StonedEdge/Retro-Lite-CM4/CAD Files/Housing/Screen Bezel Dimensions (Glass - Tempered).PNG

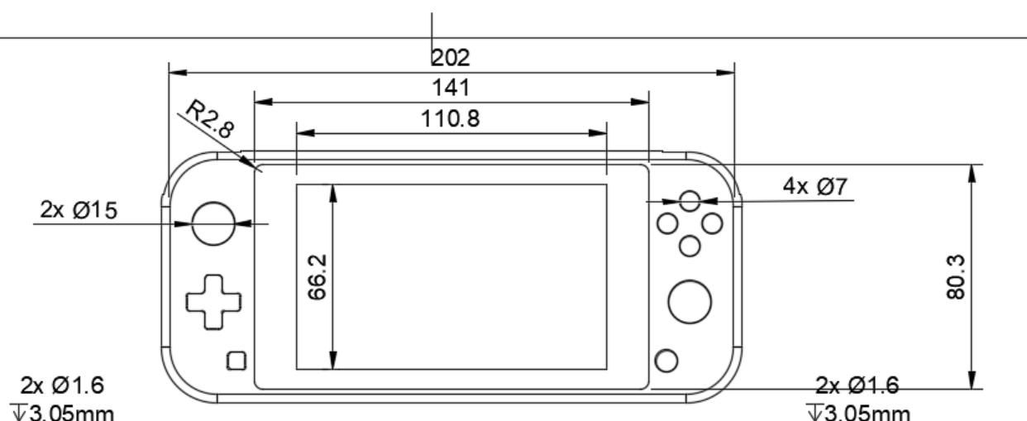
CAD Files/Housing/Screen Bezel Dimensions (Glass - Tempered).PNG
