StonedEdge/Retro-Lite-CM4/keyboard/00.png

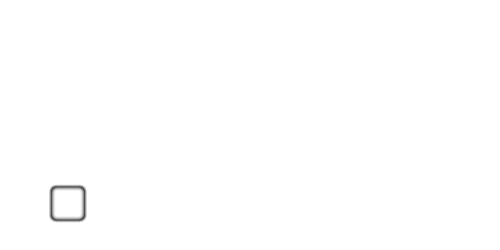
keyboard/00.png
