StonedEdge/Retro-Lite-CM4/keyboard/02.png

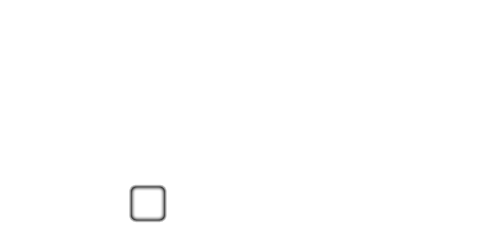
keyboard/02.png
