StonedEdge/Retro-Lite-CM4/keyboard/03.png

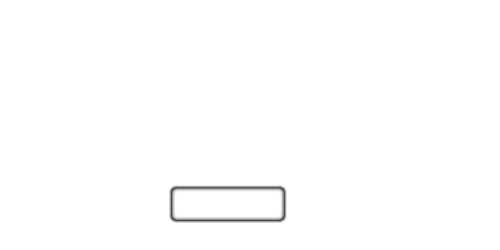
keyboard/03.png
