StonedEdge/Retro-Lite-CM4/keyboard/05.png

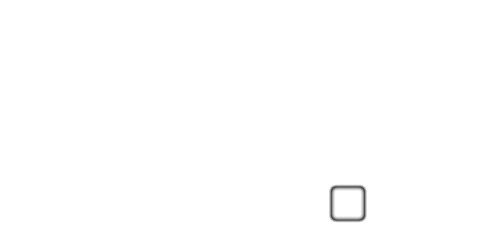
keyboard/05.png
