StonedEdge/Retro-Lite-CM4/keyboard/06.png

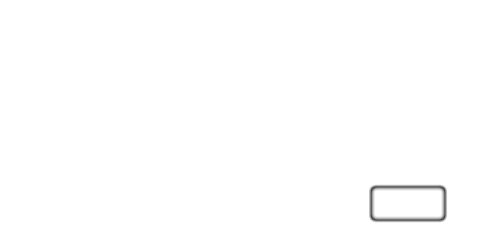
keyboard/06.png
