StonedEdge/Retro-Lite-CM4/keyboard/11.png

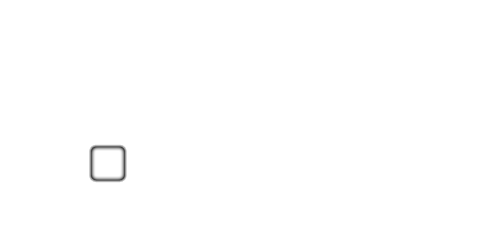
keyboard/11.png
