StonedEdge/Retro-Lite-CM4/keyboard/13.png

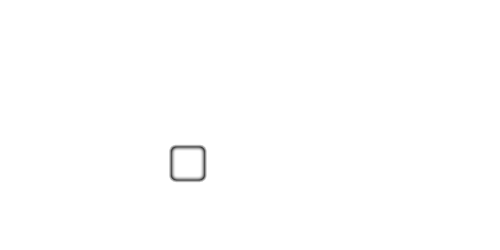
keyboard/13.png
