StonedEdge/Retro-Lite-CM4/keyboard/14.png

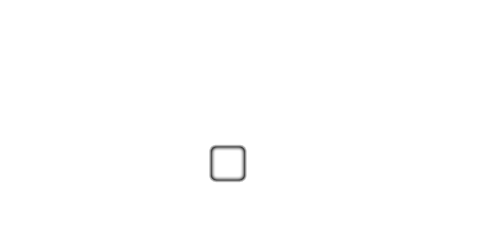
keyboard/14.png
