StonedEdge/Retro-Lite-CM4/keyboard/16.png

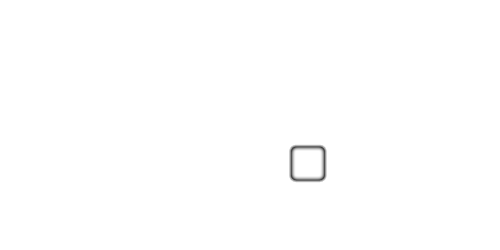
keyboard/16.png
