StonedEdge/Retro-Lite-CM4/keyboard/20.png

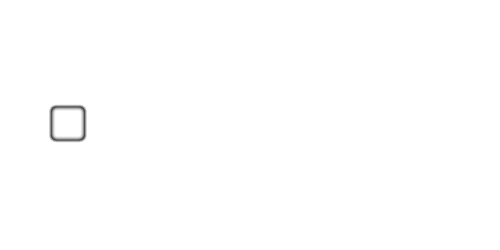
keyboard/20.png
