StonedEdge/Retro-Lite-CM4/keyboard/22.png

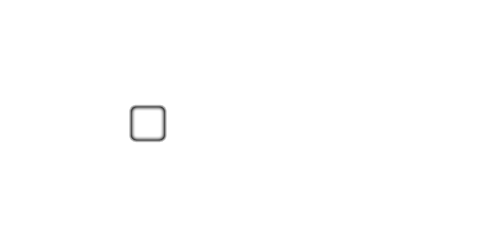
keyboard/22.png
