StonedEdge/Retro-Lite-CM4/keyboard/25.png

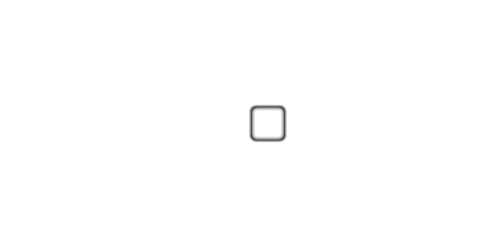
keyboard/25.png
