StonedEdge/Retro-Lite-CM4/keyboard/27.png

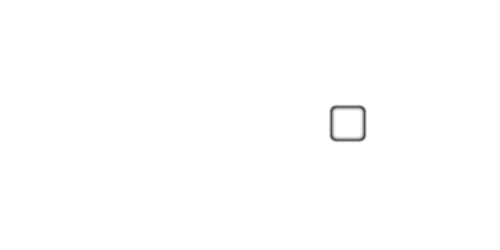
keyboard/27.png
