StonedEdge/Retro-Lite-CM4/keyboard/28.png

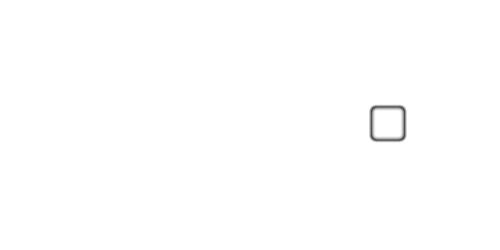
keyboard/28.png
