StonedEdge/Retro-Lite-CM4/keyboard/31.png

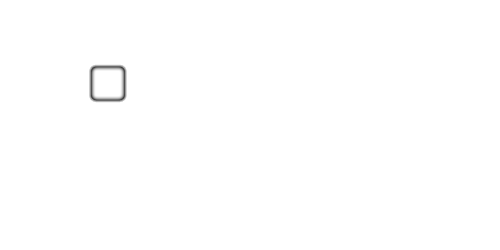
keyboard/31.png
