StonedEdge/Retro-Lite-CM4/keyboard/33.png

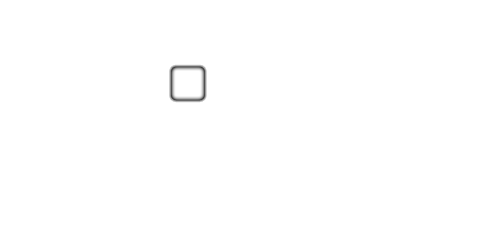
keyboard/33.png
