StonedEdge/Retro-Lite-CM4/keyboard/34.png

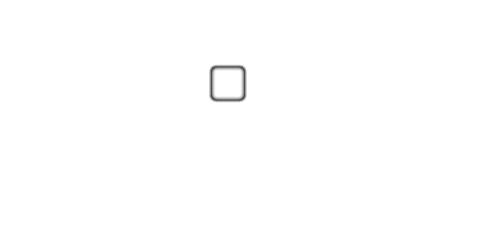
keyboard/34.png
