StonedEdge/Retro-Lite-CM4/keyboard/36.png

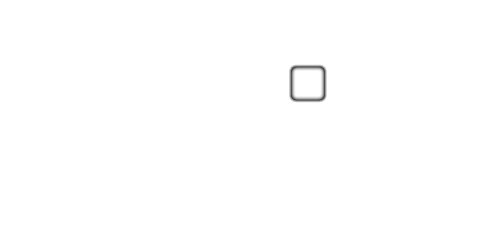
keyboard/36.png
