StonedEdge/Retro-Lite-CM4/keyboard/40.png

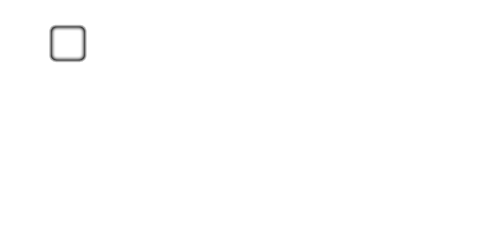
keyboard/40.png
