StonedEdge/Retro-Lite-CM4/keyboard/42.png

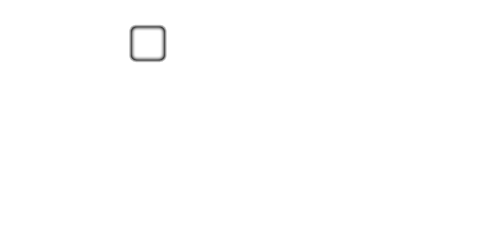
keyboard/42.png
