StonedEdge/Retro-Lite-CM4/keyboard/43.png

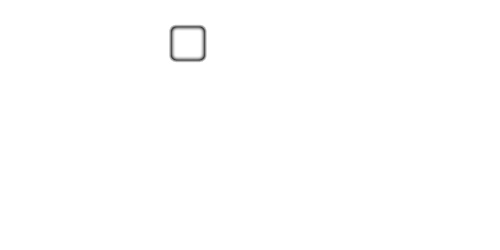
keyboard/43.png
