StonedEdge/Retro-Lite-CM4/keyboard/44.png

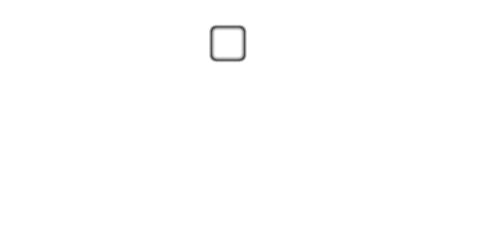
keyboard/44.png
