StonedEdge/Retro-Lite-CM4/keyboard/46.png

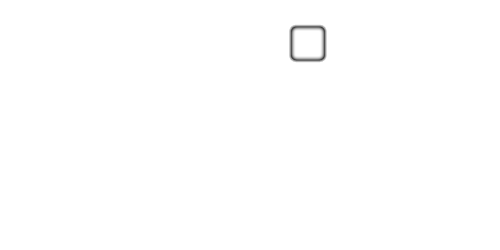
keyboard/46.png
