StonedEdge/Retro-Lite-CM4/keyboard/47.png

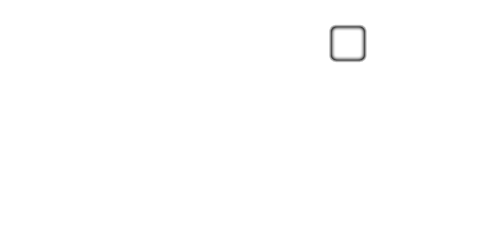
keyboard/47.png
