StonedEdge/Retro-Lite-CM4/keyboard/49.png

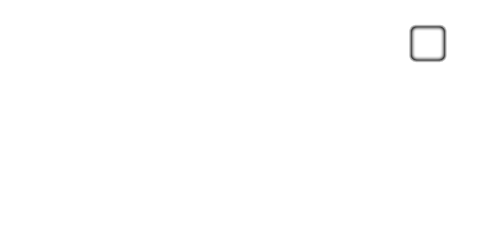
keyboard/49.png
