StonedEdge/Retro-Lite-CM4/keyboard/lowerCase.png

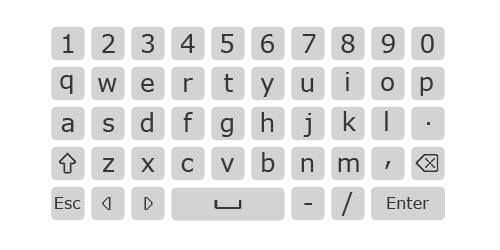
keyboard/lowerCase.png
