StonedEdge/Retro-Lite-CM4/overlays/batteryInfo.png

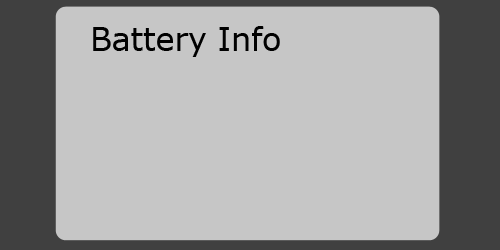
overlays/batteryInfo.png
