StonedEdge/Retro-Lite-CM4/overlays/lowbatterywarning.png

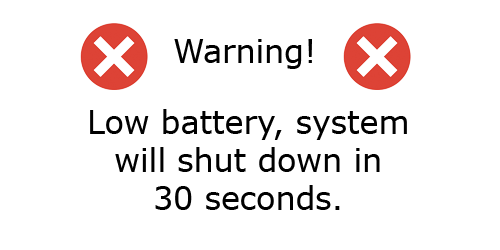
overlays/lowbatterywarning.png
