StonedEdge/Retro-Lite-CM4/overlays/mainMenu.png

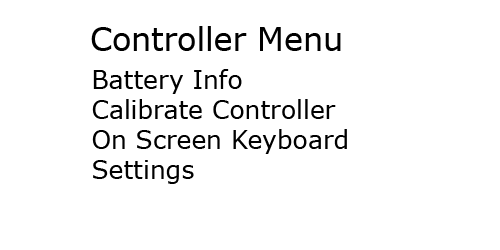
overlays/mainMenu.png
