StonedEdge/Retro-Lite-CM4/overlays/settingsMenu.png

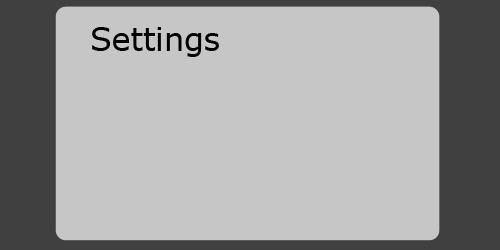
overlays/settingsMenu.png
